ChrisPVille/RL02/uC/ucpins.c

//*****************************************************************************
// Copyright (c) 2014 Texas Instruments Incorporated.  All rights reserved.
// Software License Agreement
//
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
//   Redistributions of source code must retain the above copyright
//   notice, this list of conditions and the following disclaimer.
//
//   Redistributions in binary form must reproduce the above copyright
//   notice, this list of conditions and the following disclaimer in the
//   documentation and/or other materials provided with the
//   distribution.
//
//   Neither the name of Texas Instruments Incorporated nor the names of
//   its contributors may be used to endorse or promote products derived
//   from this software without specific prior written permission.
//
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
// This file was automatically generated by the Tiva C Series PinMux Utility
// Version: 1.0.4
//
//*****************************************************************************

#include <stdint.h>
#include <stdbool.h>
#include "ucpins.h"
#include "inc/hw_types.h"
#include "inc/hw_memmap.h"
#include "inc/hw_gpio.h"
#include "driverlib/sysctl.h"
#include "driverlib/pin_map.h"
#include "driverlib/rom_map.h"
#include "driverlib/gpio.h"

//*****************************************************************************
void
PortFunctionInit(void)
{
    //
    // Enable Peripheral Clocks
    //
    MAP_SysCtlPeripheralEnable(SYSCTL_PERIPH_SSI0);
    MAP_SysCtlPeripheralEnable(SYSCTL_PERIPH_UART0);
    MAP_SysCtlPeripheralEnable(SYSCTL_PERIPH_USB0);
    MAP_SysCtlPeripheralEnable(SYSCTL_PERIPH_GPIOA);
    MAP_SysCtlPeripheralEnable(SYSCTL_PERIPH_GPIOD);
    MAP_SysCtlPeripheralEnable(SYSCTL_PERIPH_GPIOF);

    //
    // Enable pin PA7 for GPIOInput
    //
    MAP_GPIOPinTypeGPIOInput(GPIO_PORTA_BASE, GPIO_PIN_7);

    //
    // Enable pin PA6 for GPIOInput - SPI Current Word is Header Word
    //
    MAP_GPIOPinTypeGPIOInput(GPIO_PORTA_BASE, GPIO_PIN_6);

    //
    // Enable pin PF2 for GPIOInput
    //
    MAP_GPIOPinTypeGPIOInput(GPIO_PORTF_BASE, GPIO_PIN_2);

    //
    // Enable pin PF3 for GPIOInput
    //
    MAP_GPIOPinTypeGPIOInput(GPIO_PORTF_BASE, GPIO_PIN_3);

    //
    // Enable pin PF1 for GPIOOutputOD
    //
    MAP_GPIOPinTypeGPIOOutputOD(GPIO_PORTF_BASE, GPIO_PIN_1);

    //
    // Enable pin PA5 for SSI0 SSI0TX
    //
    MAP_GPIOPinConfigure(GPIO_PA5_SSI0TX);
    MAP_GPIOPinTypeSSI(GPIO_PORTA_BASE, GPIO_PIN_5);

    //
    // Enable pin PA4 for SSI0 SSI0RX
    //
    MAP_GPIOPinConfigure(GPIO_PA4_SSI0RX);
    MAP_GPIOPinTypeSSI(GPIO_PORTA_BASE, GPIO_PIN_4);

    //
    // Enable pin PA2 for SSI0 SSI0CLK
    //
    MAP_GPIOPinConfigure(GPIO_PA2_SSI0CLK);
    MAP_GPIOPinTypeSSI(GPIO_PORTA_BASE, GPIO_PIN_2);

    //
    // Enable pin PA3 for SSI0 SSI0FSS
    //
    MAP_GPIOPinConfigure(GPIO_PA3_SSI0FSS);
    MAP_GPIOPinTypeSSI(GPIO_PORTA_BASE, GPIO_PIN_3);

    //
    // Enable pin PA0 for UART0 U0RX
    //
    MAP_GPIOPinConfigure(GPIO_PA0_U0RX);
    MAP_GPIOPinTypeUART(GPIO_PORTA_BASE, GPIO_PIN_0);

    //
    // Enable pin PA1 for UART0 U0TX
    //
    MAP_GPIOPinConfigure(GPIO_PA1_U0TX);
    MAP_GPIOPinTypeUART(GPIO_PORTA_BASE, GPIO_PIN_1);

    //
    // Enable pin PD4 for USB0 USB0DM
    //
    MAP_GPIOPinTypeUSBAnalog(GPIO_PORTD_BASE, GPIO_PIN_4);

    //
    // Enable pin PD5 for USB0 USB0DP
    //
    MAP_GPIOPinTypeUSBAnalog(GPIO_PORTD_BASE, GPIO_PIN_5);
}
